nikezi623/dolphin_robot_arm/海豚机械臂STL文件/旋转底座.STL

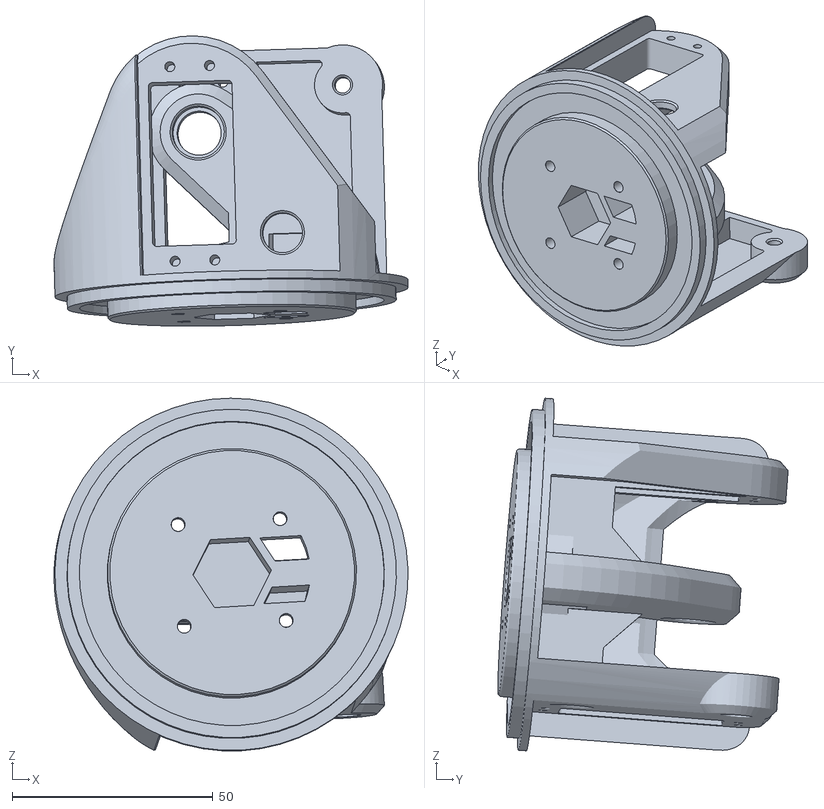
[picture p21: CAD file, 2025-09-01]
海豚机械臂STL文件/旋转底座.STL
88.2 x 72.3 x 87.8
