nikezi623/dolphin_robot_arm/海豚机械臂STL文件/B轴舵机舵盘定位块.STL

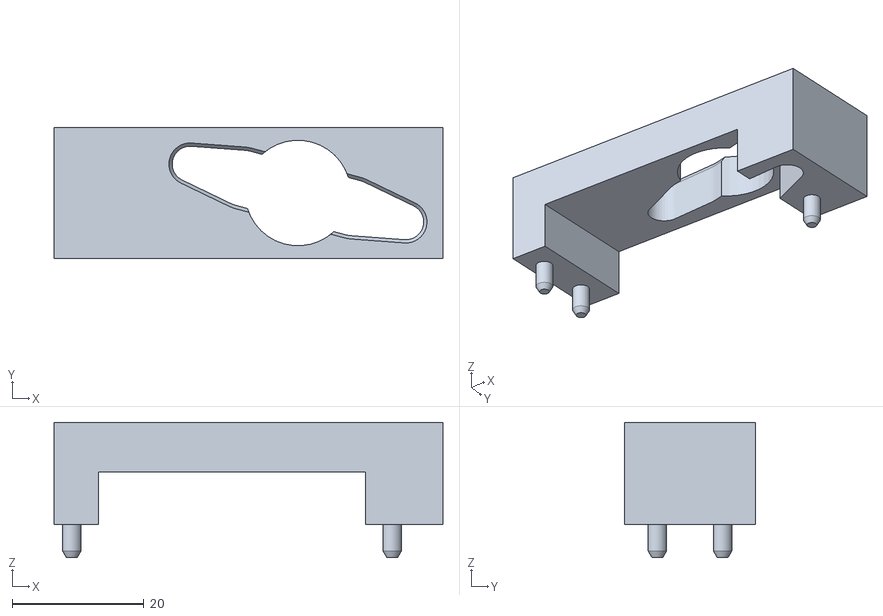
[picture p22: CAD file, 2025-09-01]
海豚机械臂STL文件/B轴舵机舵盘定位块.STL
59.0 x 19.9 x 20.5
