nikezi623/dolphin_robot_arm/海豚机械臂STL文件/夹爪主动齿.STL

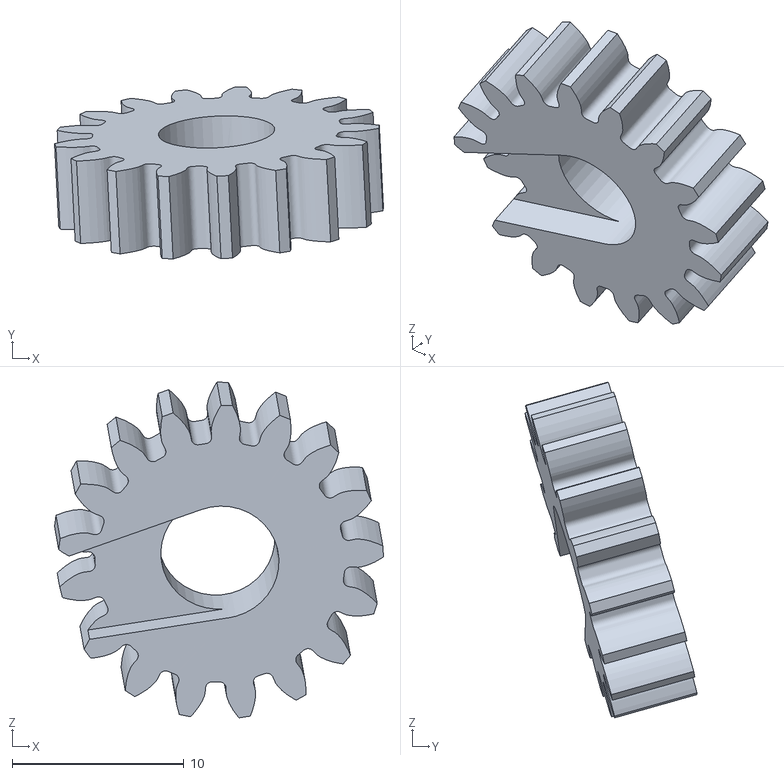
[picture p23: CAD file, 2025-09-01]
海豚机械臂STL文件/夹爪主动齿.STL
19.2 x 10.0 x 19.6
