nikezi623/dolphin_robot_arm/海豚机械臂STL文件/BC连杆.STL

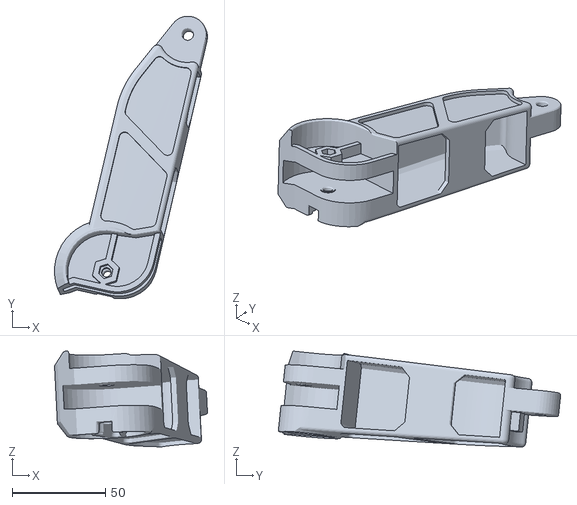
[picture p24: CAD file, 2025-09-01]
海豚机械臂STL文件/BC连杆.STL
82.1 x 151.6 x 51.4
