nikezi623/dolphin_robot_arm/海豚机械臂STL文件/A轴压块.STL

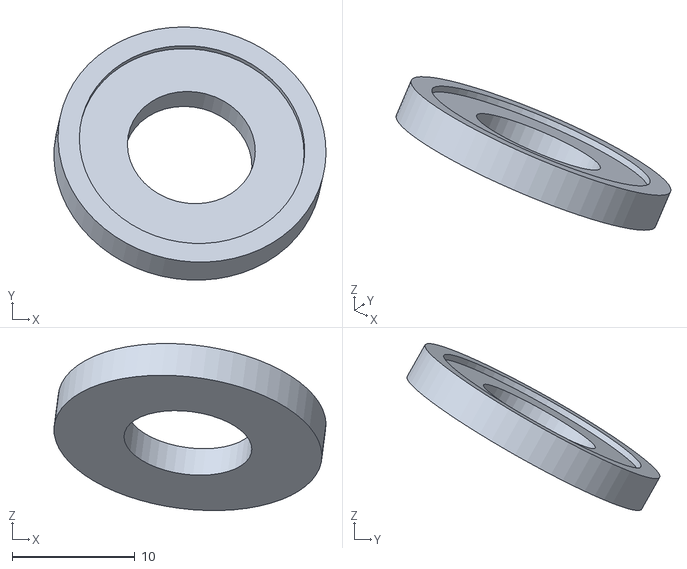
[picture p25: CAD file, 2025-09-01]
海豚机械臂STL文件/A轴压块.STL
22.2 x 20.6 x 13.6
