nikezi623/dolphin_robot_arm/海豚机械臂STL文件/旋转底座大同步带轮.STL

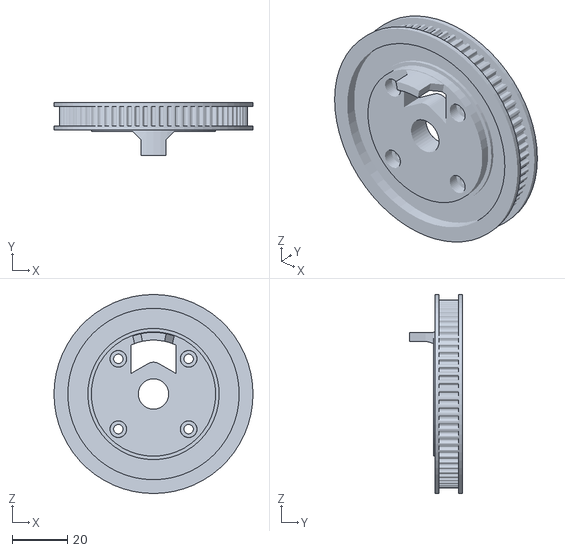
[picture p26: CAD file, 2025-09-01]
海豚机械臂STL文件/旋转底座大同步带轮.STL
72.0 x 19.3 x 72.0
