nikezi623/dolphin_robot_arm/ps2控制机械臂代码/Hardware/PWM.c

#include "stm32f10x.h"                  // Device header

void PWM_Init(void)
{
	RCC_APB1PeriphClockCmd(RCC_APB1Periph_TIM2, ENABLE);
	RCC_APB1PeriphClockCmd(RCC_APB1Periph_TIM3, ENABLE);
	RCC_APB2PeriphClockCmd(RCC_APB2Periph_GPIOA, ENABLE);
	RCC_APB2PeriphClockCmd(RCC_APB2Periph_GPIOB, ENABLE);
	
	GPIO_InitTypeDef GPIO_InitStruct;
	GPIO_InitStruct.GPIO_Mode = GPIO_Mode_AF_PP;
	GPIO_InitStruct.GPIO_Pin = GPIO_Pin_1 | GPIO_Pin_2;
	GPIO_InitStruct.GPIO_Speed = GPIO_Speed_50MHz;
	GPIO_Init(GPIOA, &GPIO_InitStruct);
	
	GPIO_InitStruct.GPIO_Mode = GPIO_Mode_AF_PP;
	GPIO_InitStruct.GPIO_Pin = GPIO_Pin_0 | GPIO_Pin_1;
	GPIO_InitStruct.GPIO_Speed = GPIO_Speed_50MHz;
	GPIO_Init(GPIOB, &GPIO_InitStruct);
	
	TIM_InternalClockConfig(TIM2);
	TIM_InternalClockConfig(TIM3);
	
	TIM_TimeBaseInitTypeDef TIM_TimeBaseInitStruct;
	TIM_TimeBaseInitStruct.TIM_ClockDivision = 1;
	TIM_TimeBaseInitStruct.TIM_CounterMode = TIM_CounterMode_Up;
	TIM_TimeBaseInitStruct.TIM_Period = 20000 - 1; //ARR
	TIM_TimeBaseInitStruct.TIM_Prescaler = 72 - 1; //PSC
	TIM_TimeBaseInitStruct.TIM_RepetitionCounter = 0;
	TIM_TimeBaseInit(TIM2, &TIM_TimeBaseInitStruct);
	TIM_TimeBaseInit(TIM3, &TIM_TimeBaseInitStruct);
	
	TIM_OCInitTypeDef TIM_OCInitStruct;
	TIM_OCStructInit(&TIM_OCInitStruct); //给上一行的结构体附初始值，避免不使用所有结构体包含的变量而产生意想不到的问题
	TIM_OCInitStruct.TIM_OCMode = TIM_OCMode_PWM1;
	TIM_OCInitStruct.TIM_OCPolarity = TIM_OCPolarity_High;
	TIM_OCInitStruct.TIM_OutputState = TIM_OutputState_Enable;
	TIM_OCInitStruct.TIM_Pulse = 0; //CCR 500-2500
	TIM_OC2Init(TIM2, &TIM_OCInitStruct);
	TIM_OC3Init(TIM2, &TIM_OCInitStruct);
	TIM_OC3Init(TIM3, &TIM_OCInitStruct);
	TIM_OC4Init(TIM3, &TIM_OCInitStruct);
	
	TIM_Cmd(TIM2, ENABLE);
	TIM_Cmd(TIM3, ENABLE);
}

void PWM_SetCompare2A(uint16_t Compare)
{
	TIM_SetCompare2(TIM2, Compare);
}

void PWM_SetCompare2B(uint16_t Compare)
{
	TIM_SetCompare3(TIM2, Compare);
}

void PWM_SetCompare3C(uint16_t Compare)
{
	TIM_SetCompare3(TIM3, Compare);
}

void PWM_SetCompare4D(uint16_t Compare)
{
	TIM_SetCompare4(TIM3, Compare);
}
