nikezi623/dolphin_robot_arm/ps2控制机械臂代码/Hardware/PWM.h

#ifndef __PWM_H
#define __PWM_H

void PWM_Init(void);
void PWM_SetCompare2A(uint16_t Compare);
void PWM_SetCompare2B(uint16_t Compare);
void PWM_SetCompare3C(uint16_t Compare);
void PWM_SetCompare4D(uint16_t Compare);

#endif
